strofos/ThrottleESP/Images/WhatsApp Image 2026-06-04 at 5.16.46 PM.jpeg

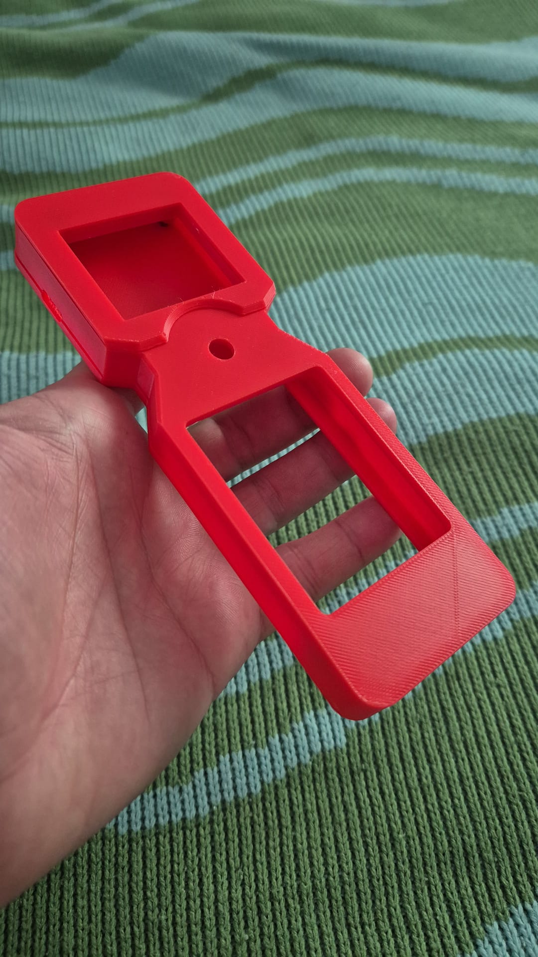
Images/WhatsApp Image 2026-06-04 at 5.16.46 PM.jpeg
