strofos/ThrottleESP/Images/WhatsApp Image 2026-06-04 at 5.17.21 PM.jpeg

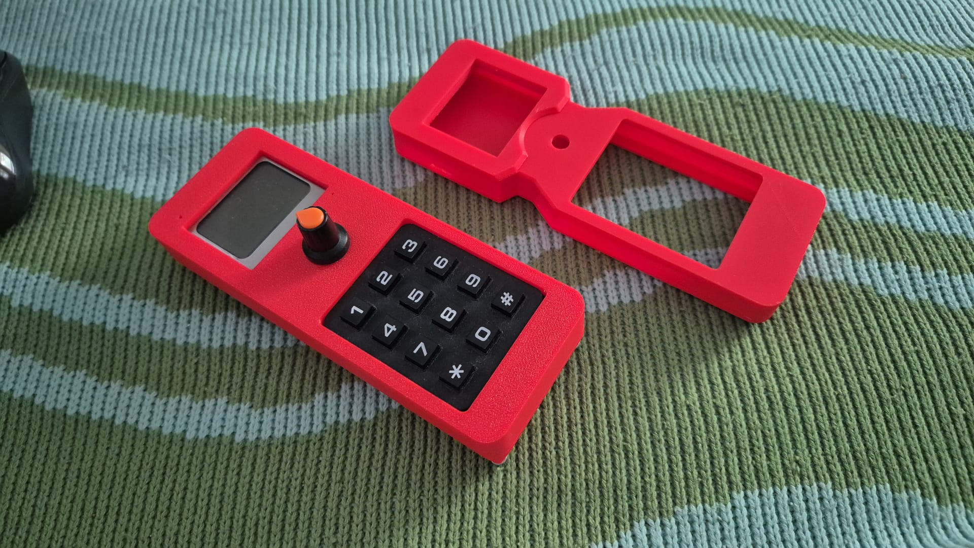
Images/WhatsApp Image 2026-06-04 at 5.17.21 PM.jpeg
