strofos/ThrottleESP/WhatsApp Image 2026-08-02 at 9.06.26 PM.jpeg

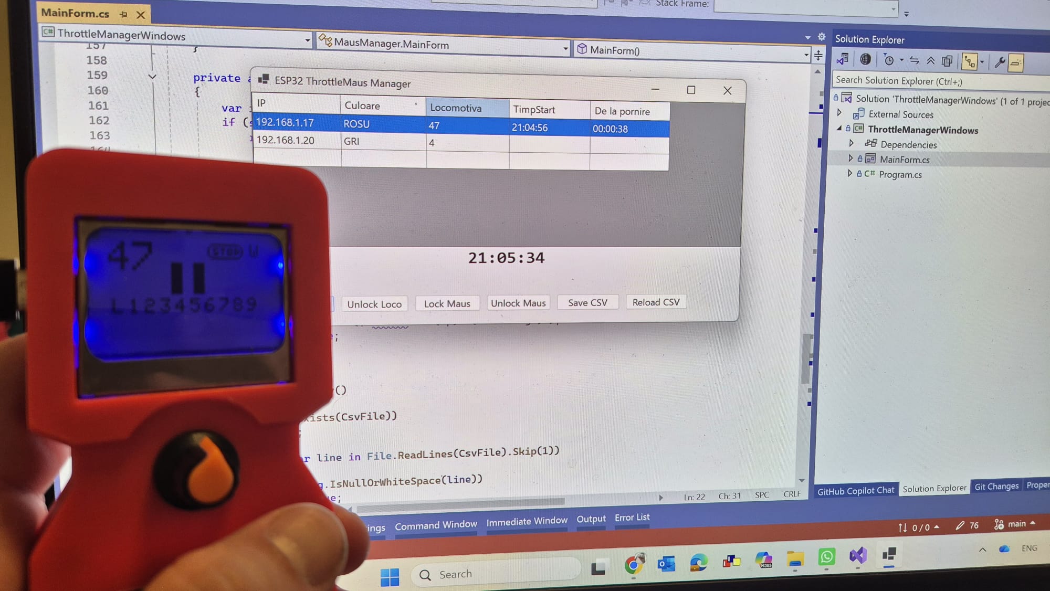
WhatsApp Image 2026-08-02 at 9.06.26 PM.jpeg
